vicente-da-silva/PowerDepot/FJElectricsPCB Common/3d packages/R1966AxxxxxxFF.stp

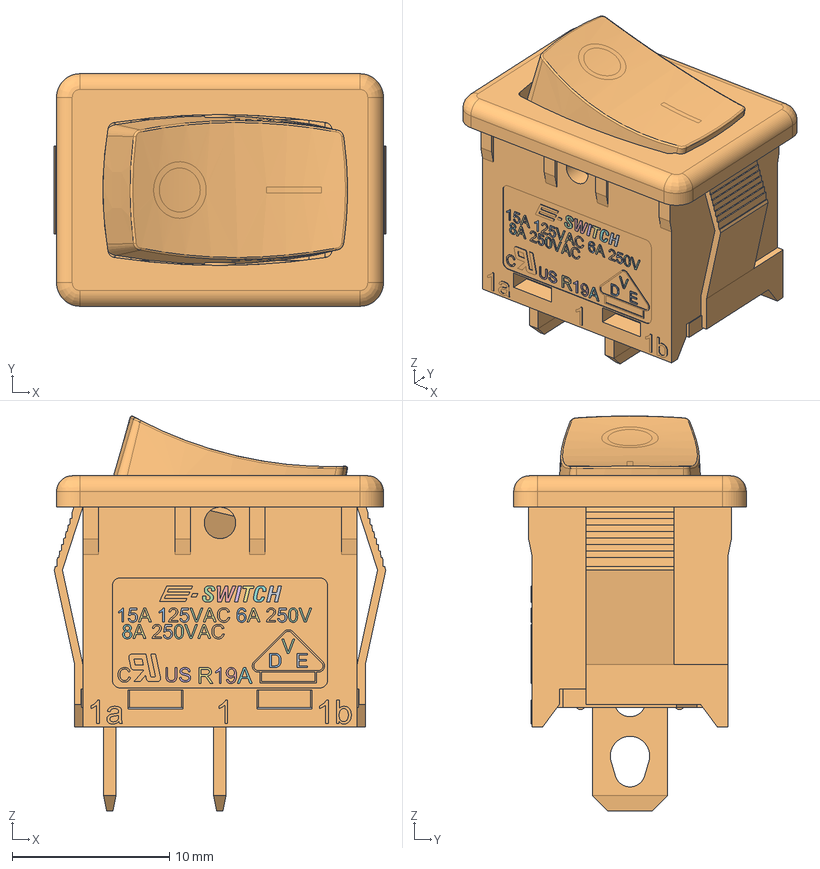
[picture p3: CAD file, 2022-01-10]
FJElectricsPCB Common/3d packages/R1966AxxxxxxFF.stp
21.1 x 14.8 x 25.1 mm
